feilipu/yaz180/docs/8255_crt_interface.png

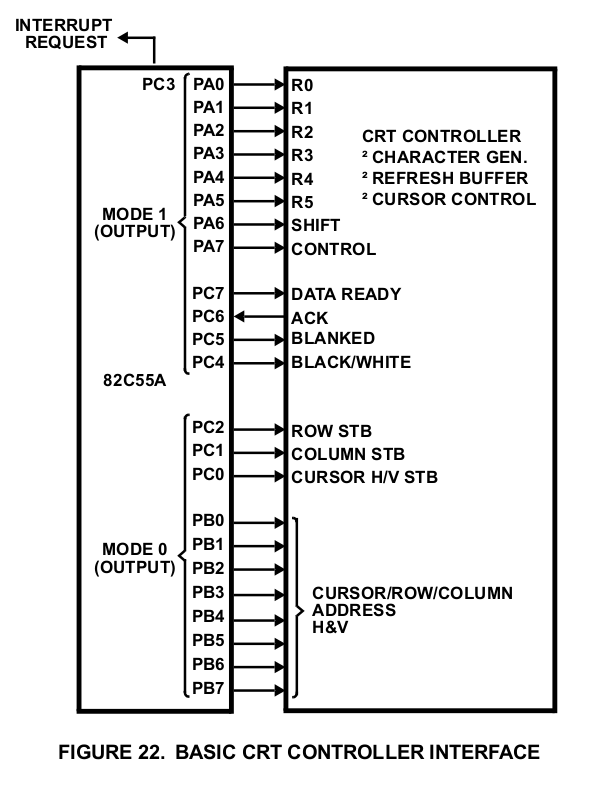
docs/8255_crt_interface.png
