feilipu/yaz180/docs/8255_floppy_disc_interface.png

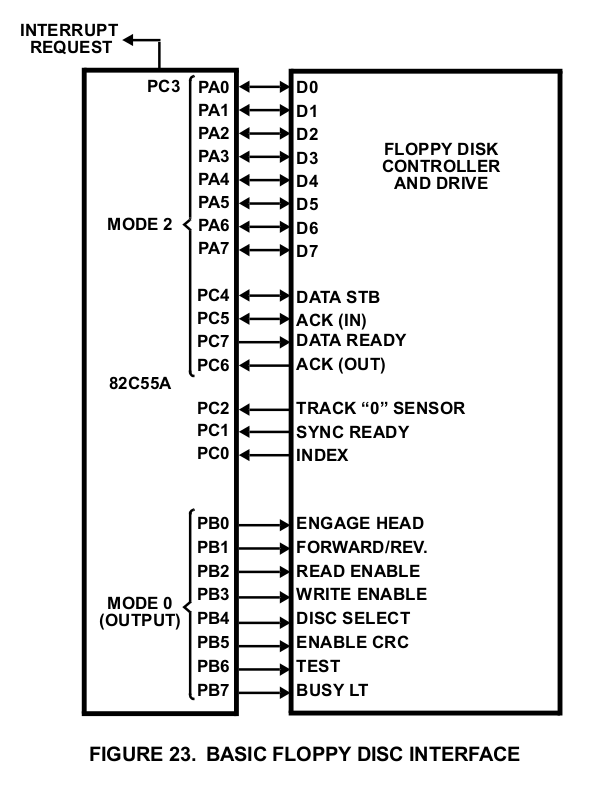
docs/8255_floppy_disc_interface.png
