feilipu/yaz180/docs/8255_keyboard_display_interface.png

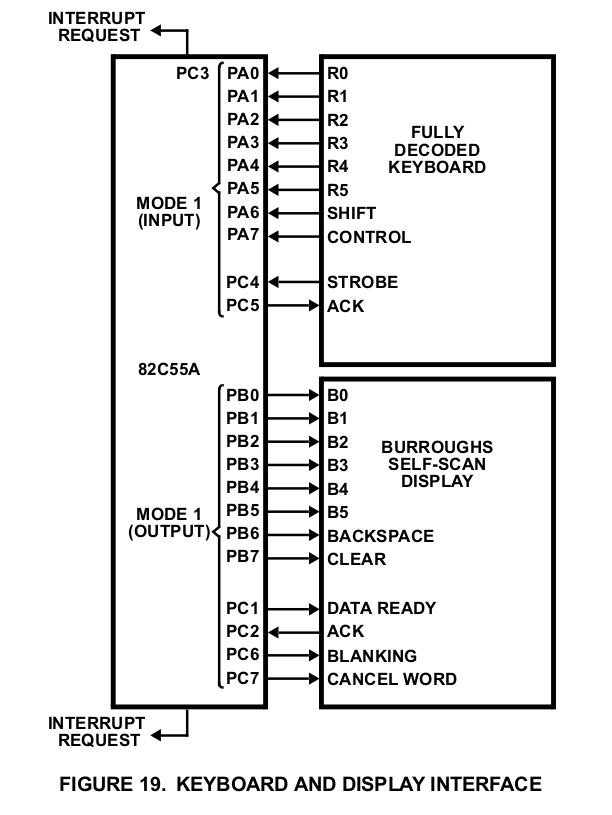
docs/8255_keyboard_display_interface.png
