feilipu/yaz180/docs/8255_keyboard_terminal_interface.png

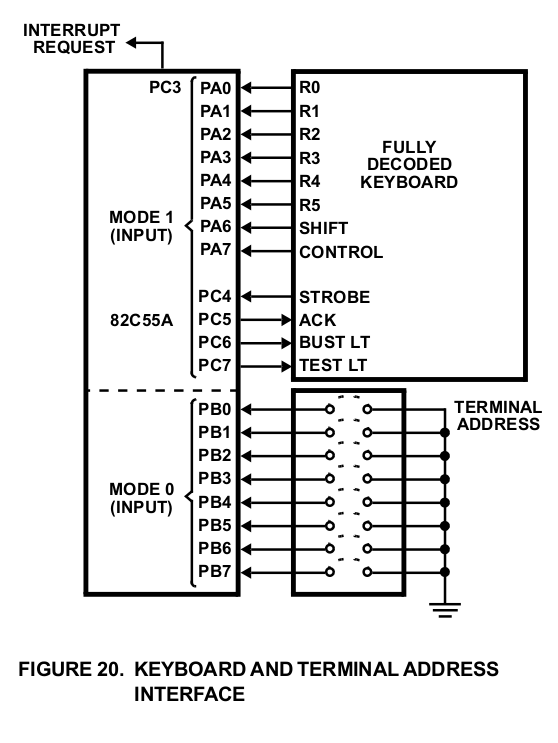
docs/8255_keyboard_terminal_interface.png
