feilipu/yaz180/docs/IMG_0698.JPG

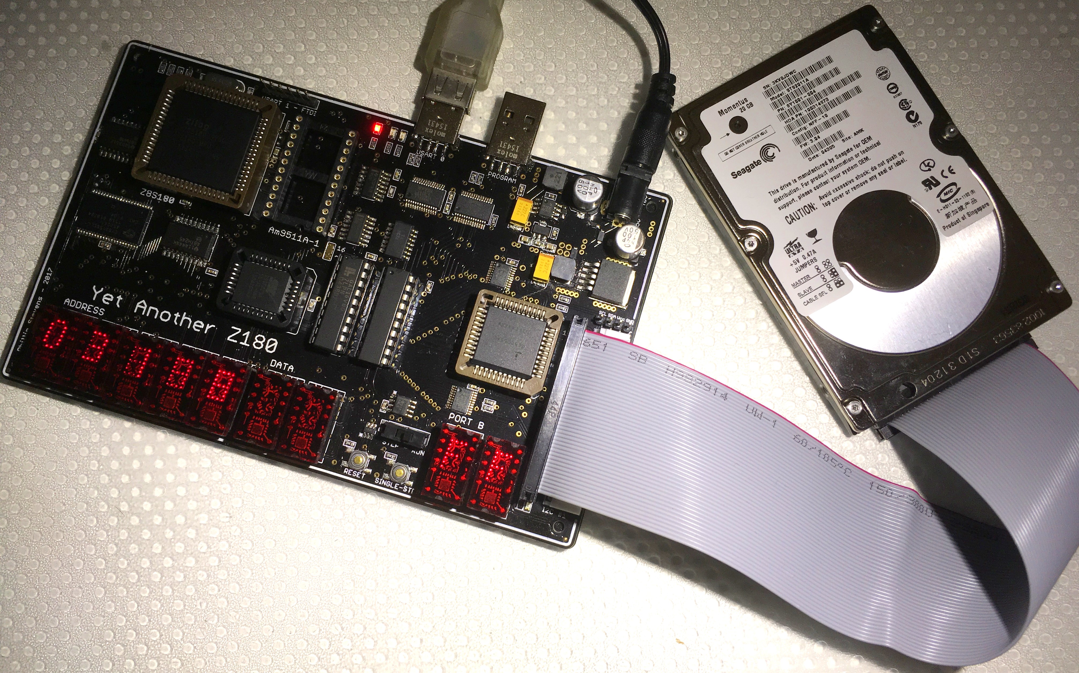
docs/IMG_0698.JPG
