feilipu/yaz180/docs/inter_bank_call.png

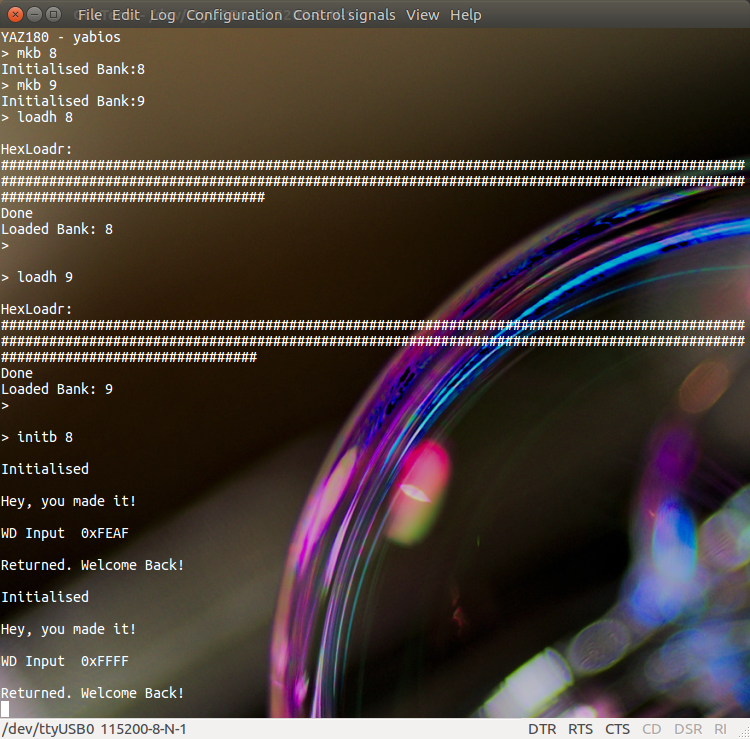
docs/inter_bank_call.png
