feilipu/yaz180/docs/LOGIC_PLD_A.png

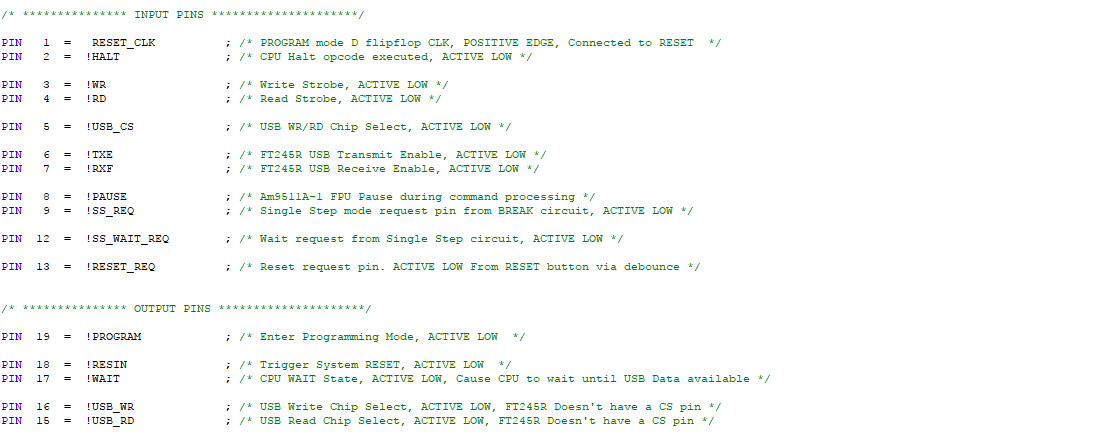
docs/LOGIC_PLD_A.png
