feilipu/yaz180/docs/LOGIC_PLD_B.png

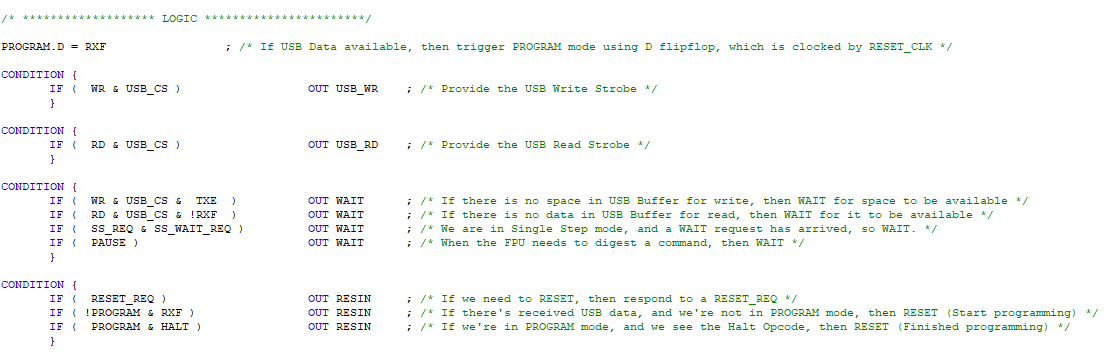
docs/LOGIC_PLD_B.png
