feilipu/yaz180/docs/MEMORY_PLD_2018_A.png

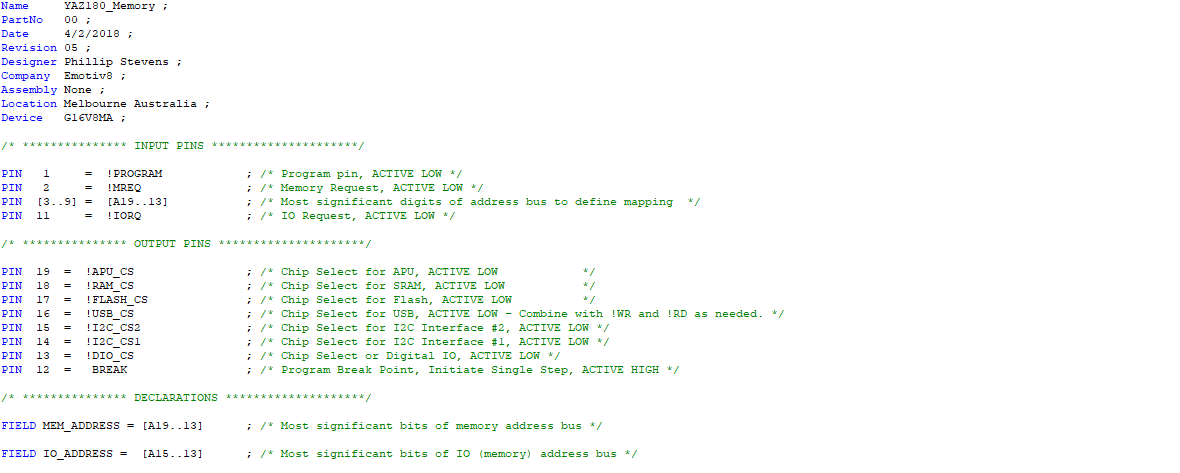
docs/MEMORY_PLD_2018_A.png
