feilipu/yaz180/docs/MEMORY_PLD_2018_B.png

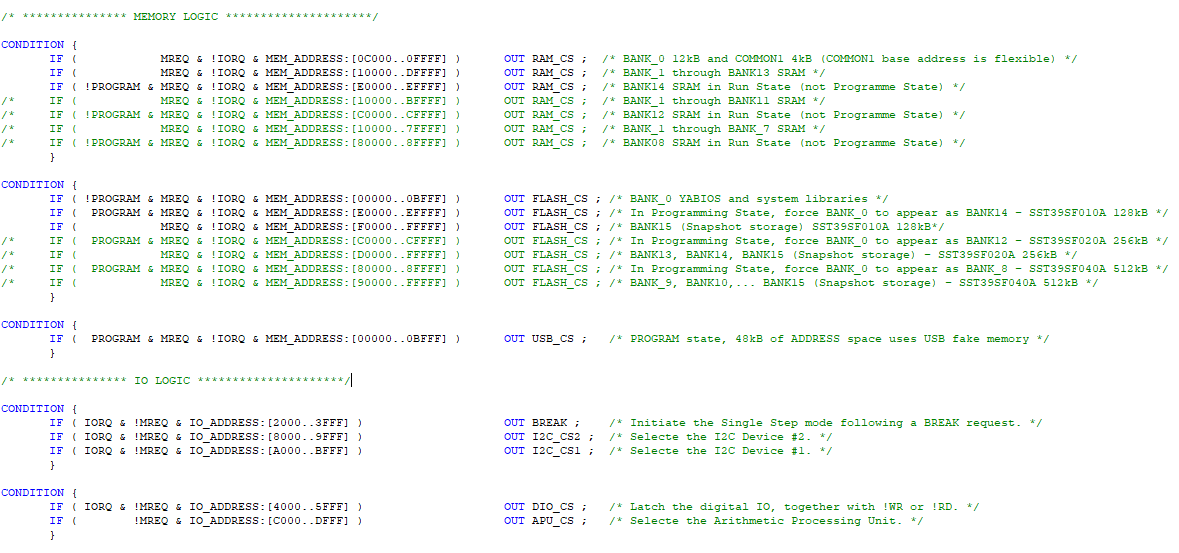
docs/MEMORY_PLD_2018_B.png
