feilipu/yaz180/docs/P1080759.JPG

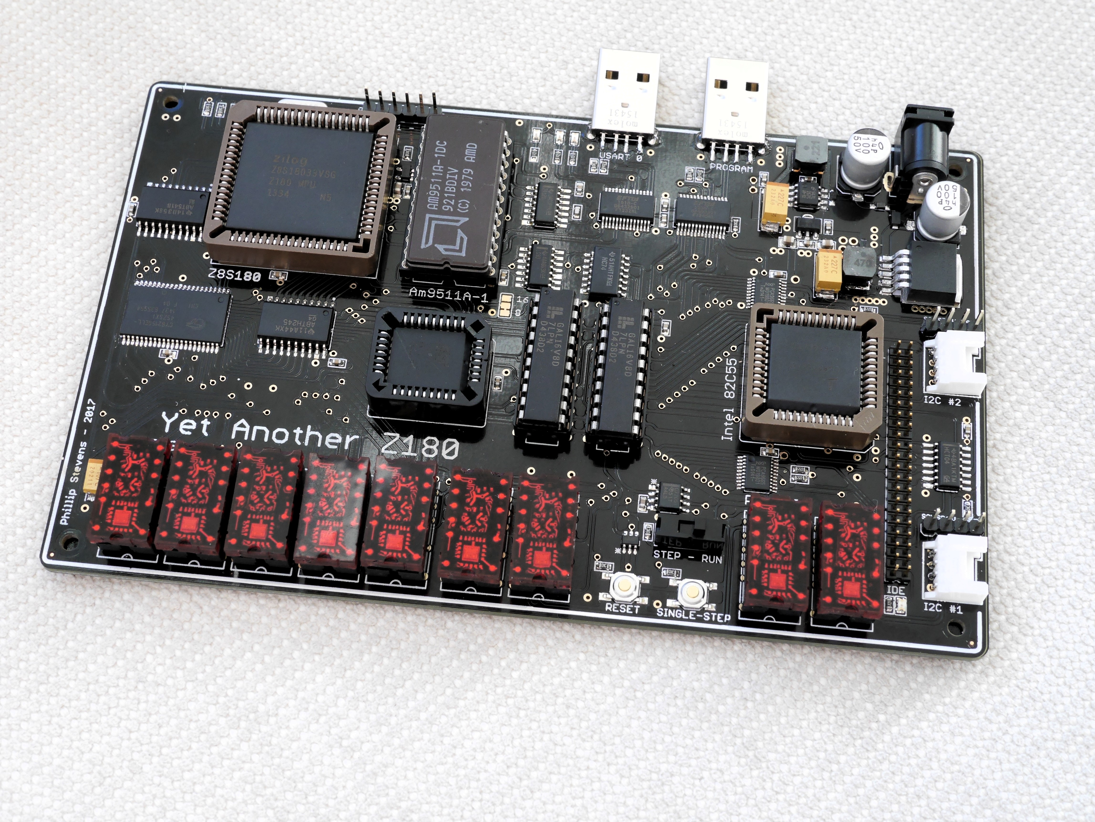
docs/P1080759.JPG
