feilipu/yaz180/docs/P1080760.JPG

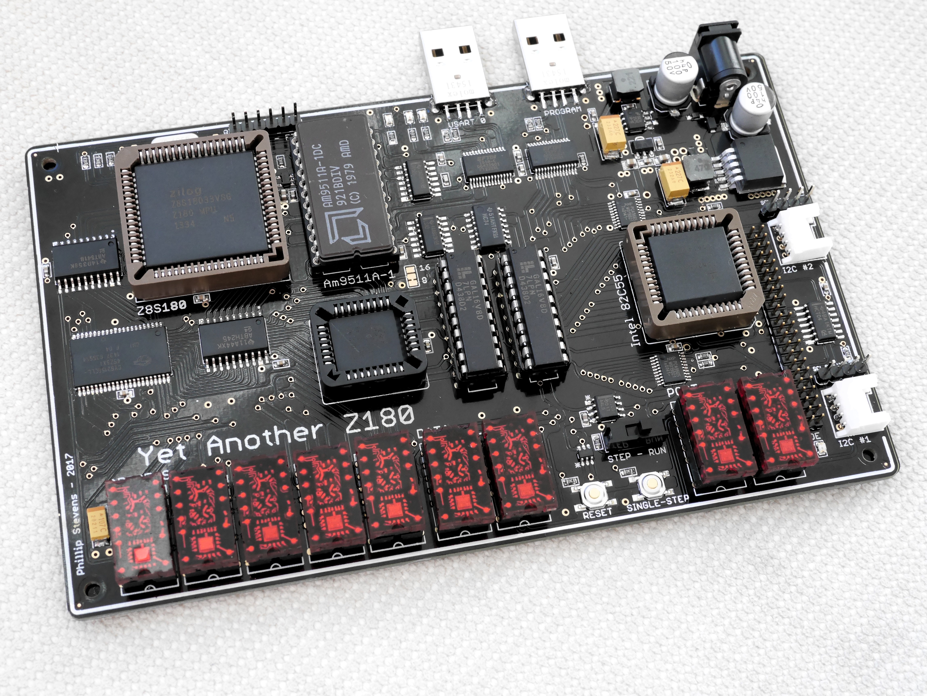
docs/P1080760.JPG
