feilipu/yaz180/docs/P1080761.JPG

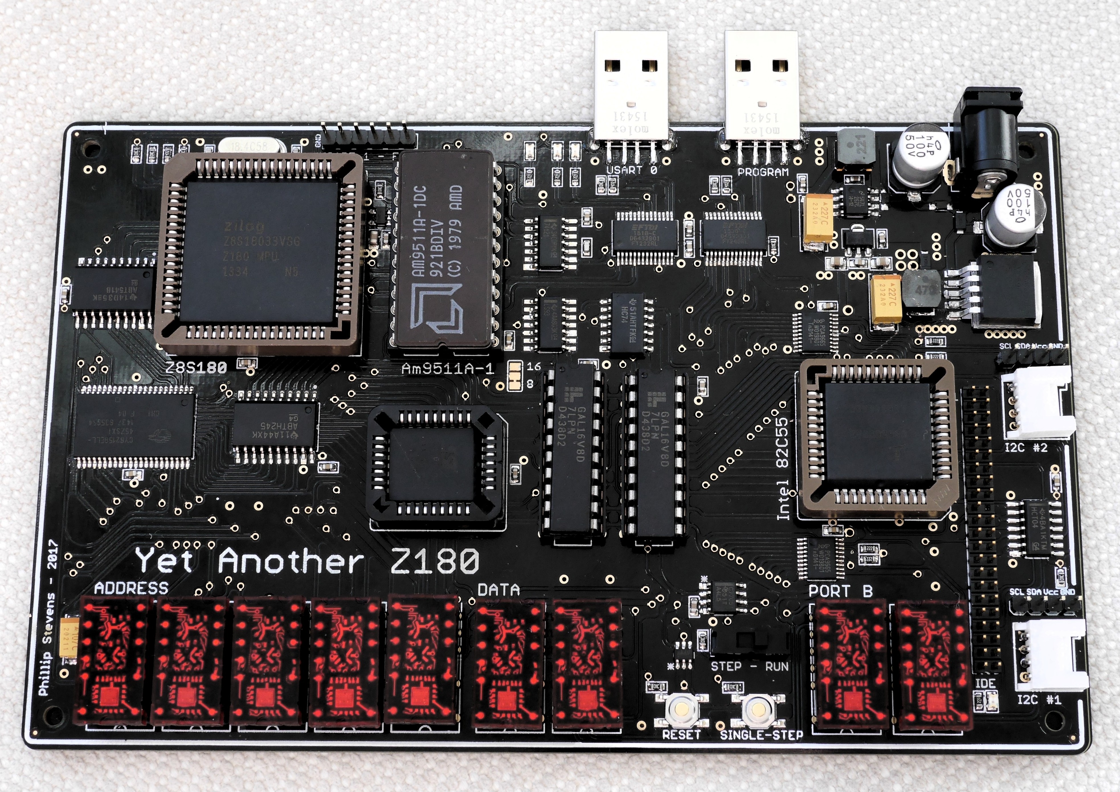
docs/P1080761.JPG
