feilipu/yaz180/docs/P1090698.JPG

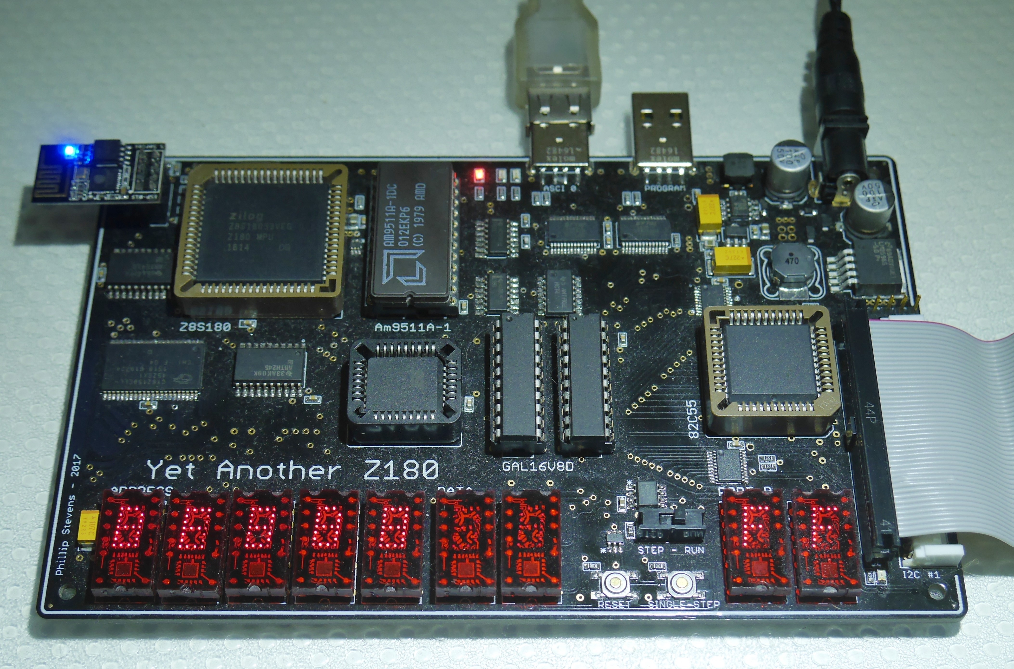
docs/P1090698.JPG
