feilipu/yaz180/docs/P1090699.JPG

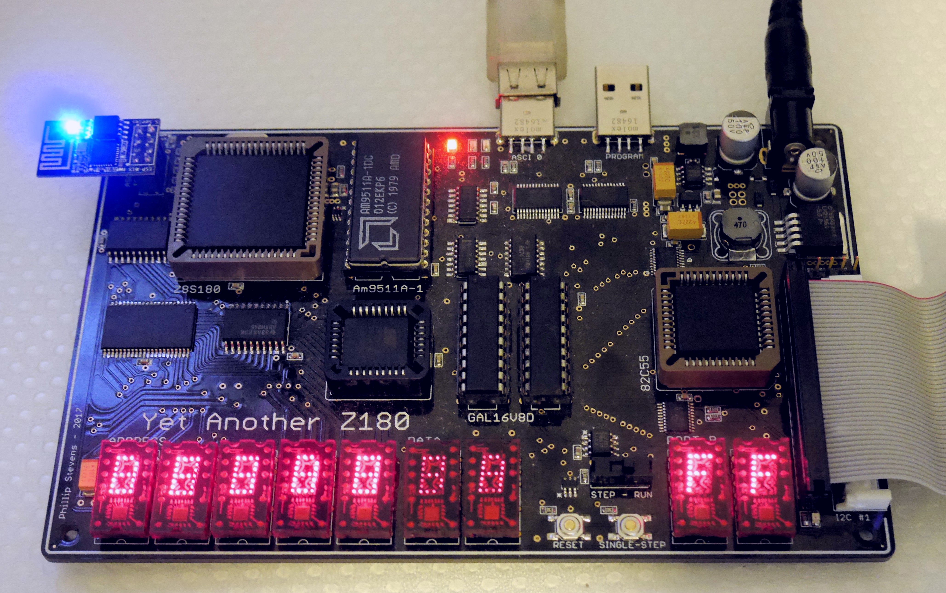
docs/P1090699.JPG
