feilipu/yaz180/docs/yaz180_cpm22.png

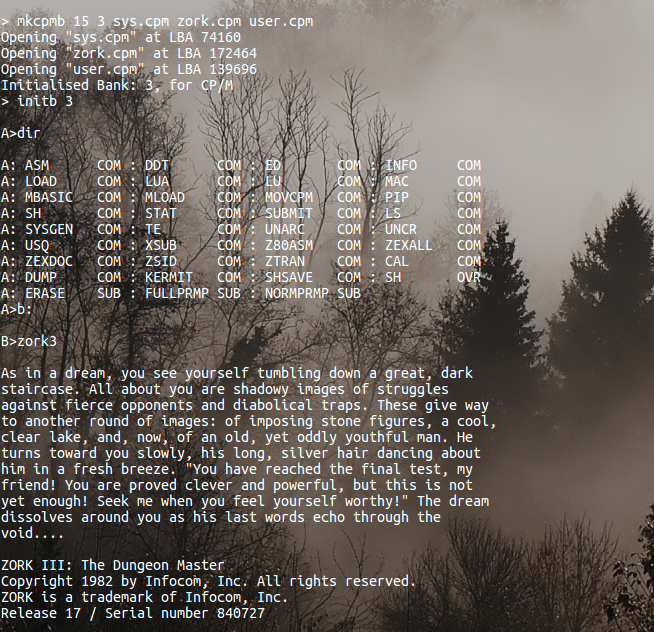
docs/yaz180_cpm22.png
