feilipu/yaz180/docs/yaz180_cpm.png

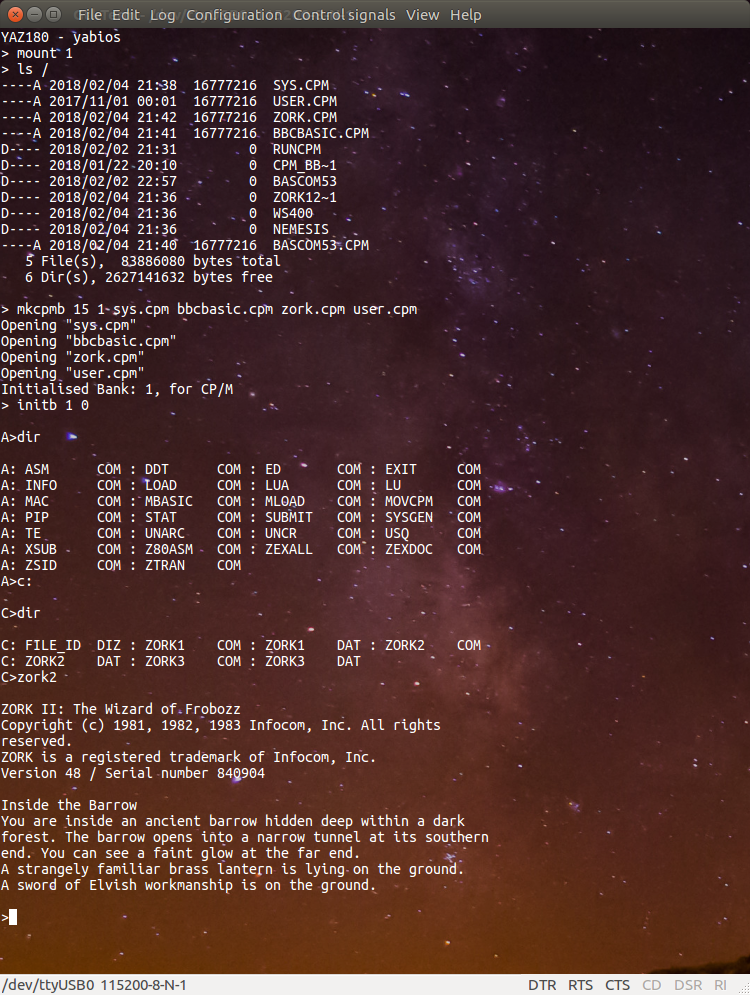
docs/yaz180_cpm.png
