feilipu/yaz180/docs/YAZ180v2.2.png

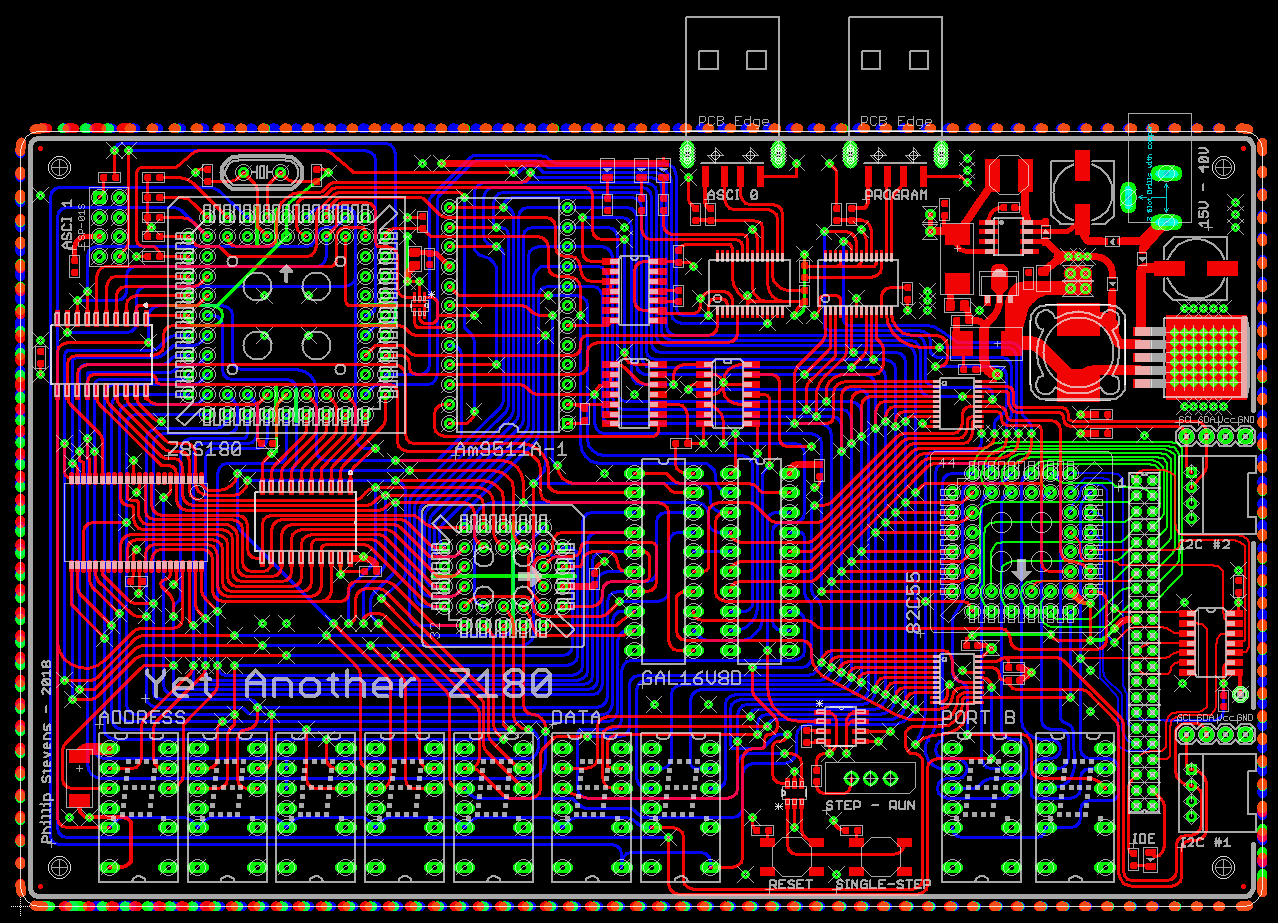
docs/YAZ180v2.2.png
