feilipu/yaz180/docs/YAZ180v21_front.JPG

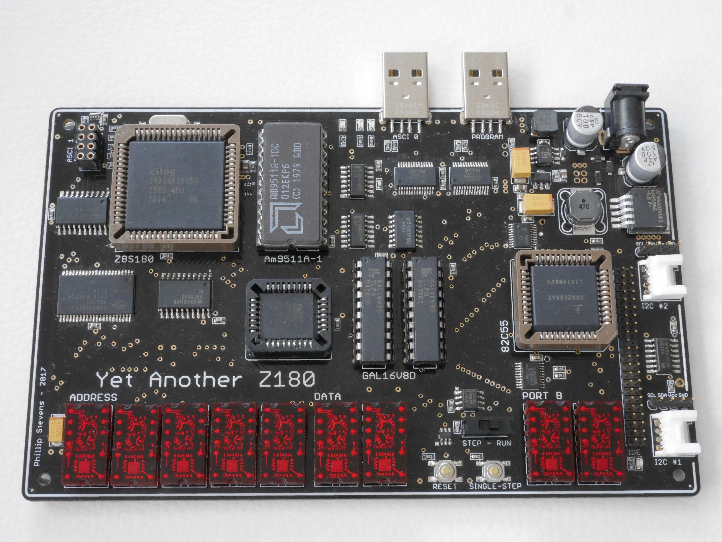
docs/YAZ180v21_front.JPG
