feilipu/yaz180/docs/YAZ180v21_left.JPG

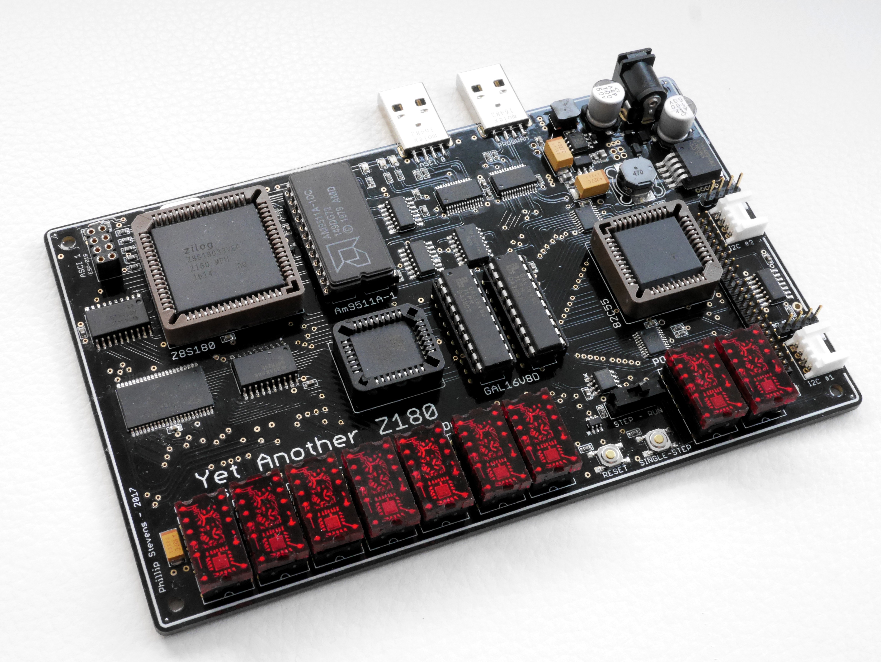
docs/YAZ180v21_left.JPG
