feilipu/yaz180/docs/YAZ180v21_left_low.JPG

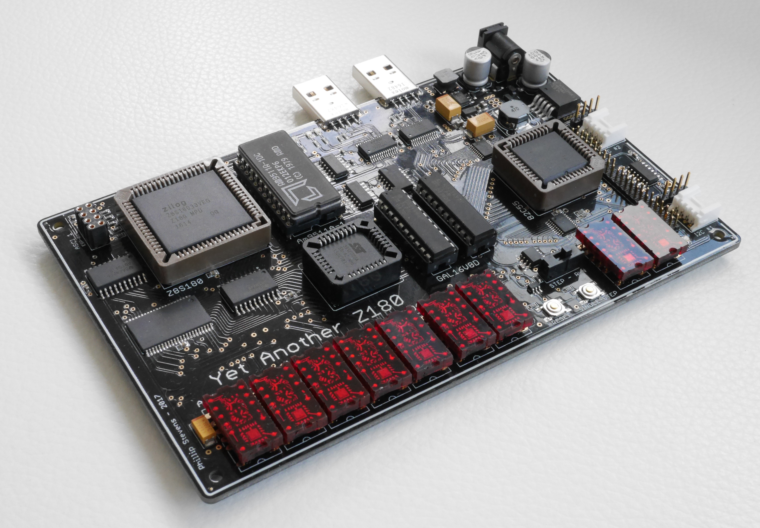
docs/YAZ180v21_left_low.JPG
