feilipu/yaz180/docs/YAZ180v21_right_low.JPG

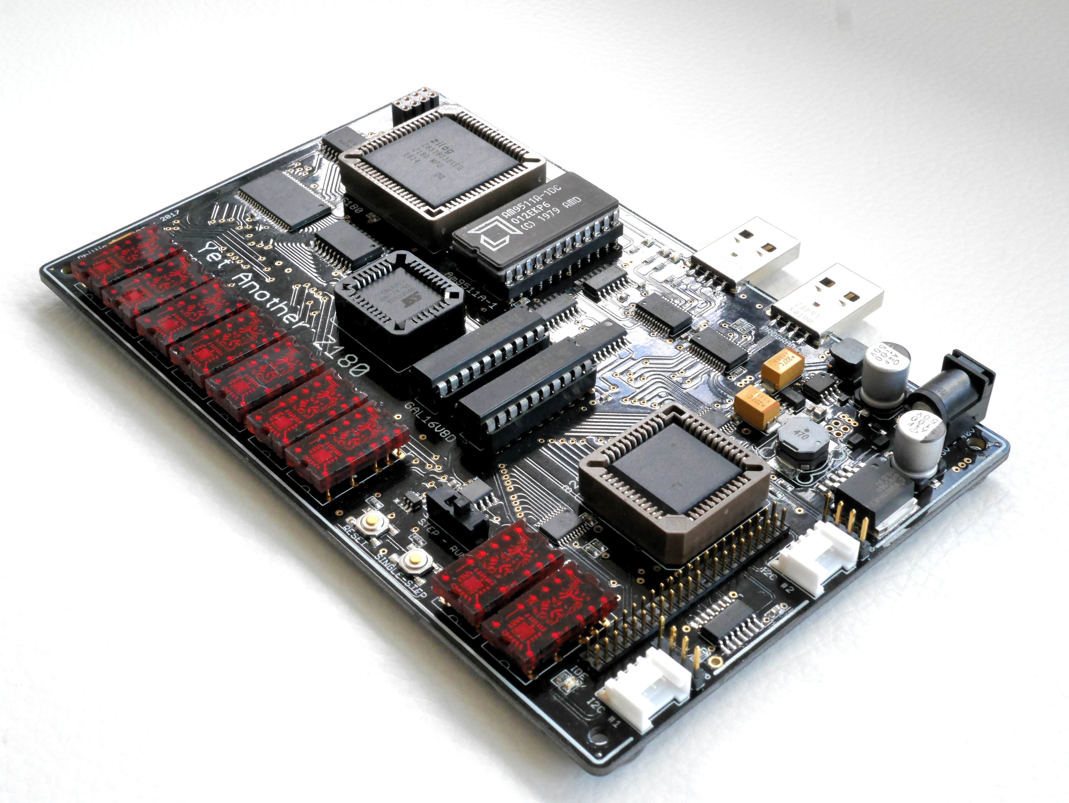
docs/YAZ180v21_right_low.JPG
