feilipu/yaz180/docs/YAZ180v21_scale.JPG

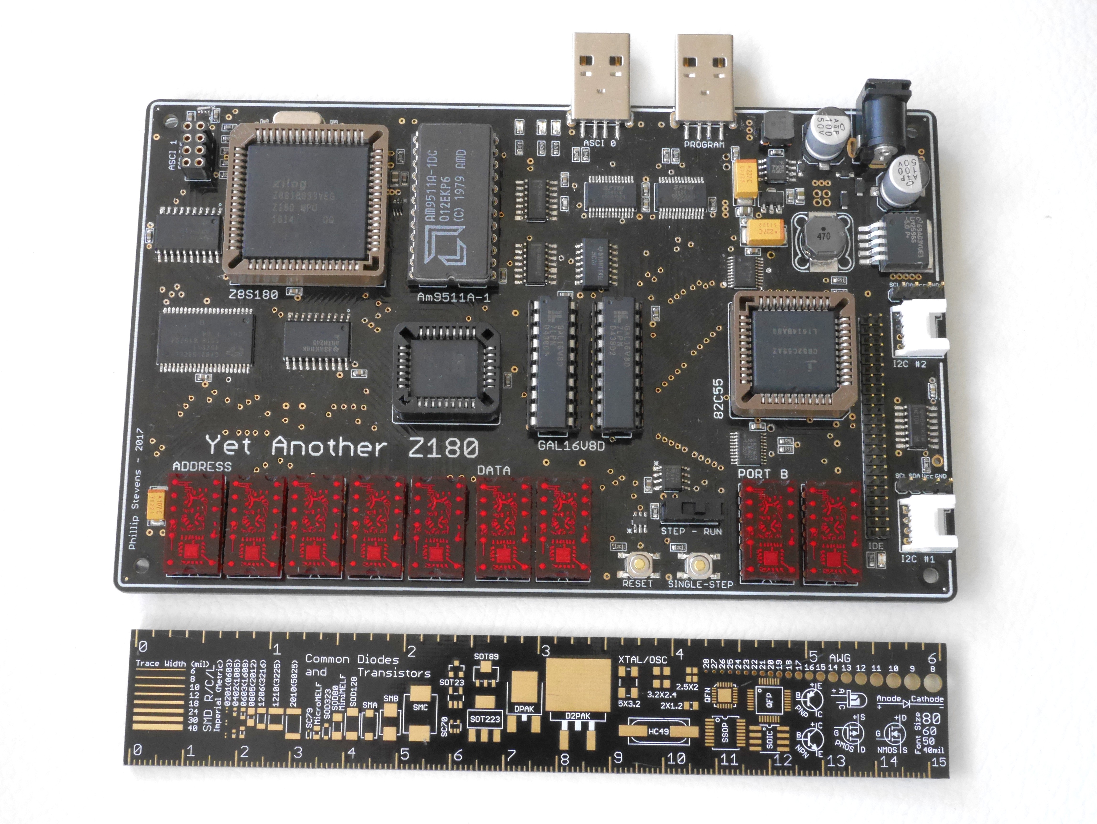
docs/YAZ180v21_scale.JPG
