feilipu/yaz180/docs/YAZ180v24_family.JPG

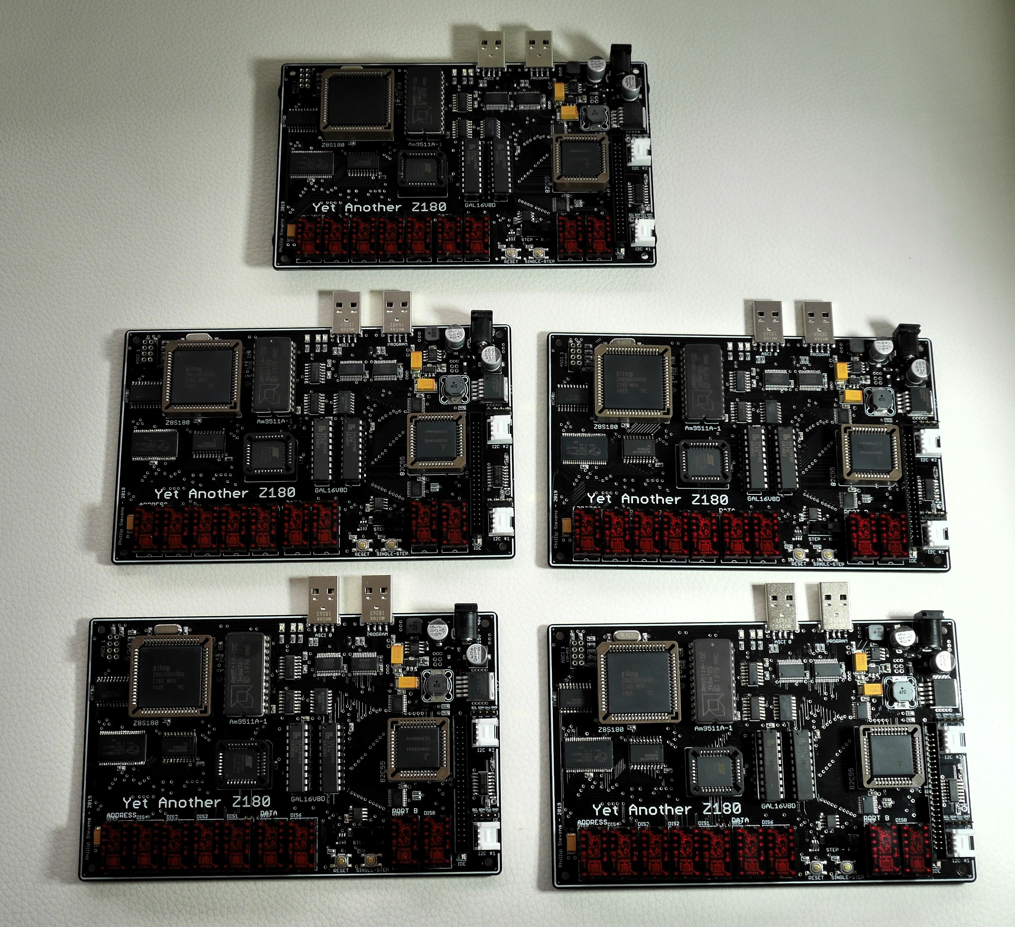
docs/YAZ180v24_family.JPG
