feilipu/yaz180/docs/YAZ180v24_front.JPG

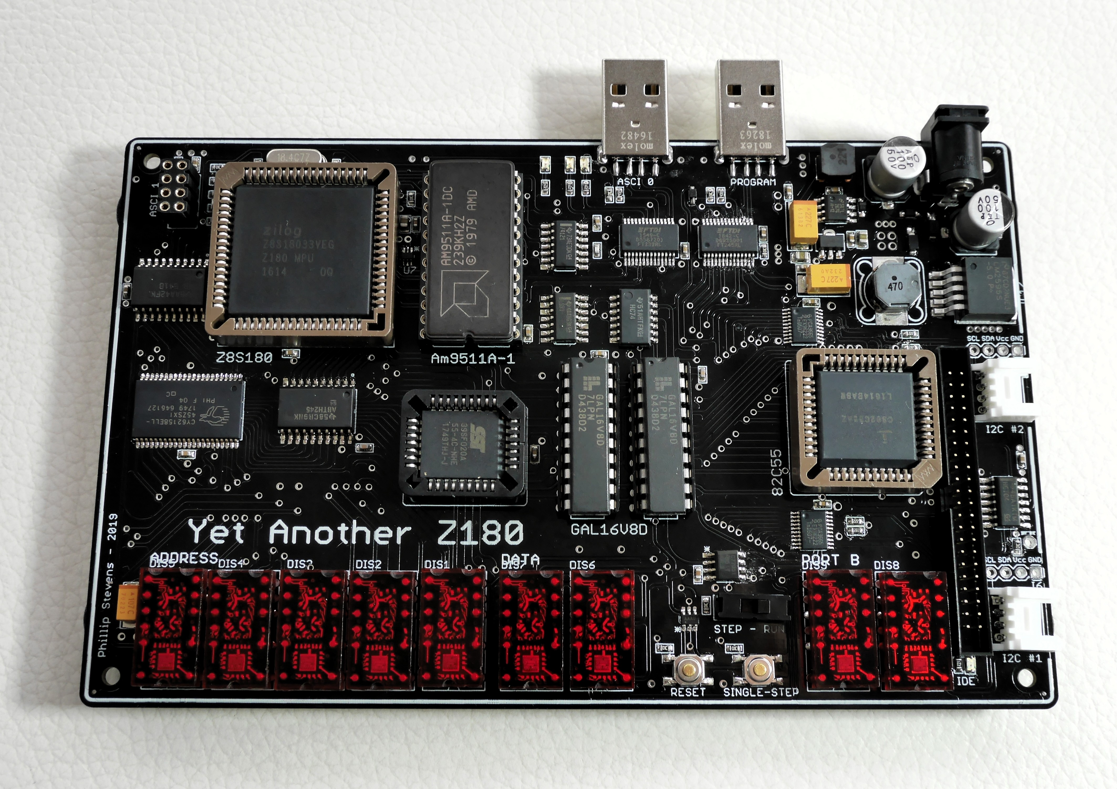
docs/YAZ180v24_front.JPG
