feilipu/yaz180/docs/8255_printer_interface.png

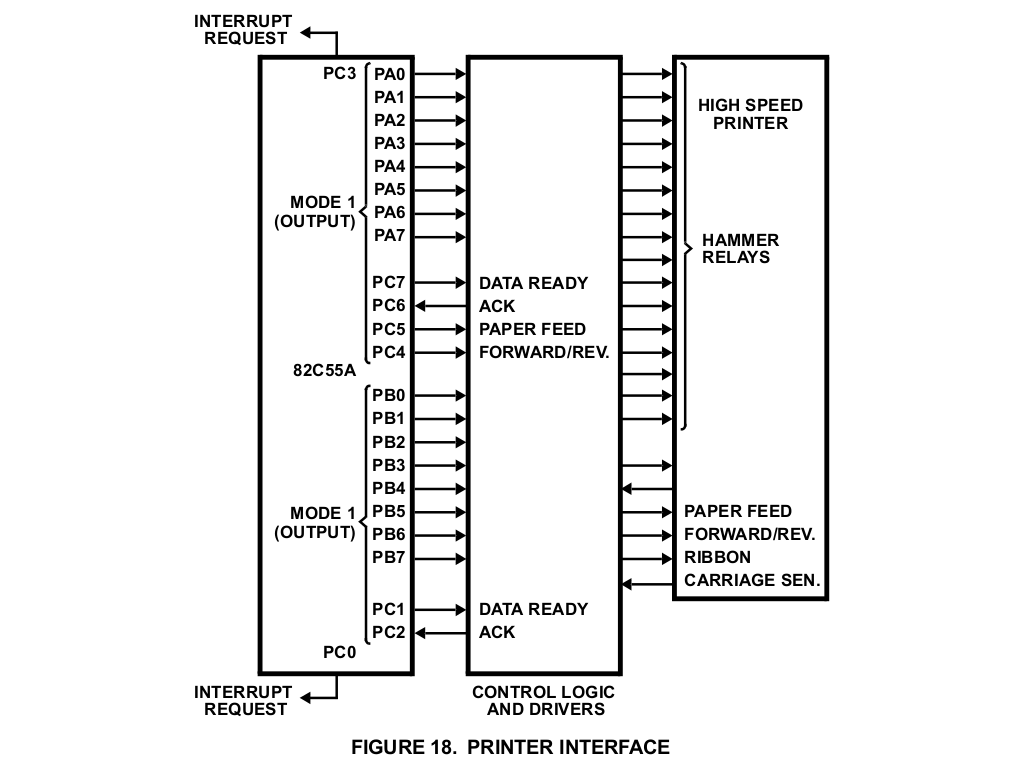
docs/8255_printer_interface.png
