feilipu/yaz180/pcb/V21_20171011/YAZ180_V21_All_Layers.pdf

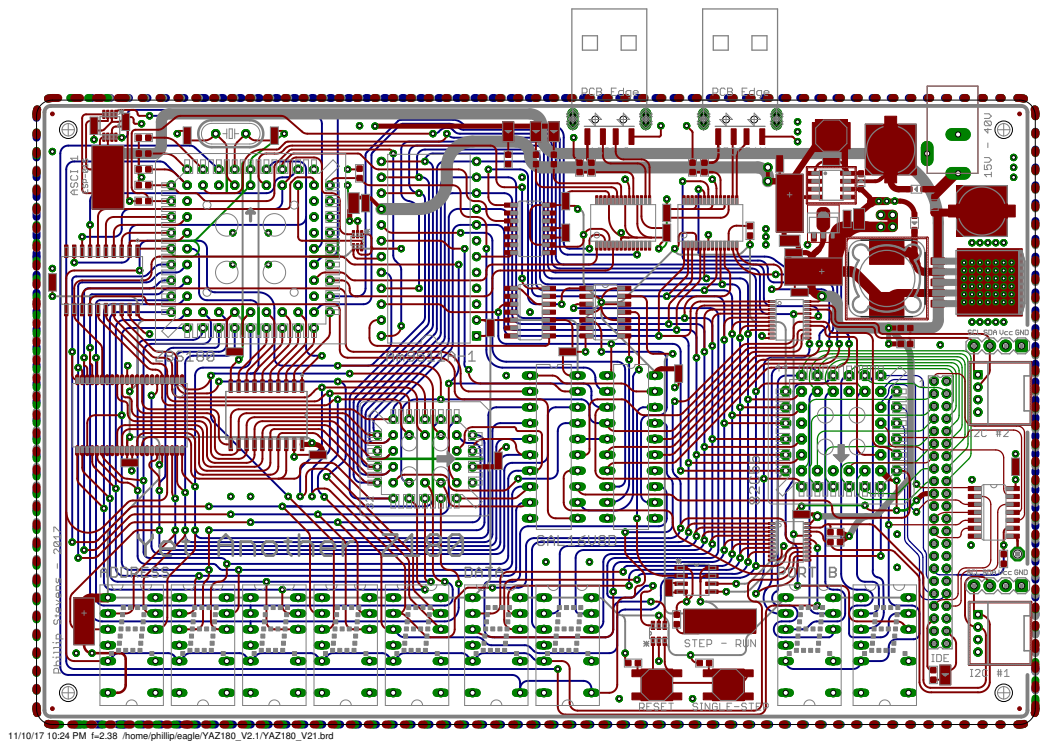
[picture p61: page 1]

11/10/17 10:24 PM f=2.38 /home/phillip/eagle/YAZ180_V2.1/YAZ180_V21.brd
