feilipu/yaz180/pcb/V21_20171011/YAZ180_V21_BottomLayer.pdf

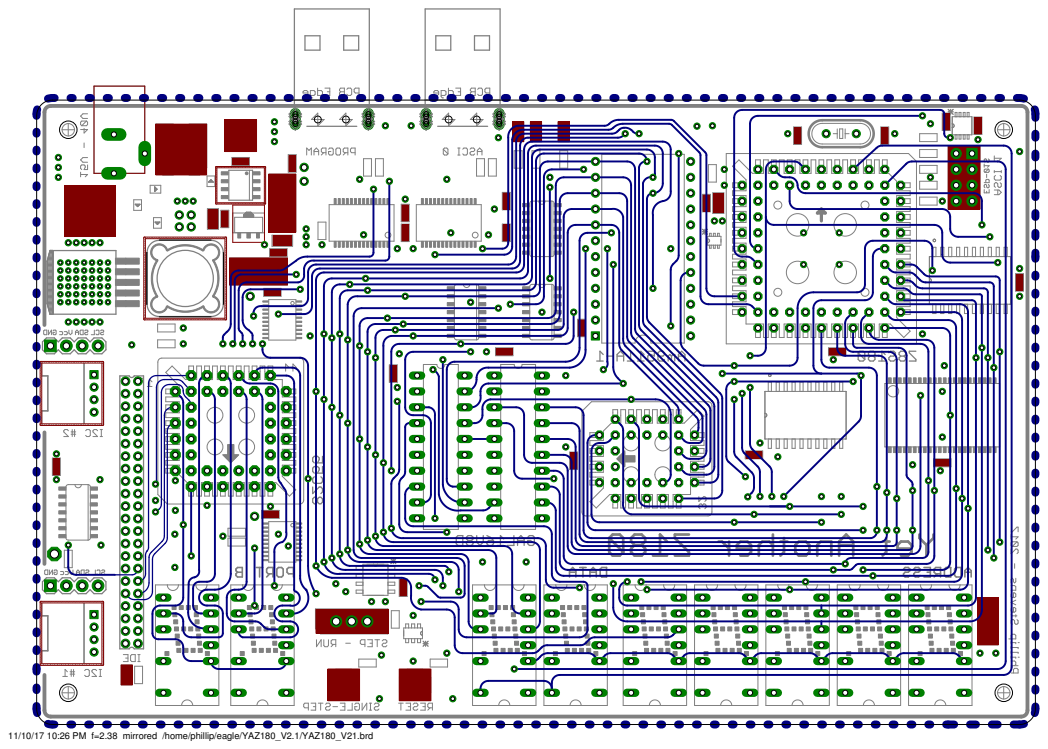
[picture p62: page 1]

11/10/17 10:26 PM f=2.38 mirrored /home/phillip/eagle/YAZ180_V2.1/YAZ180_V21.brd
