feilipu/yaz180/pcb/V21_20171011/YAZ180_V21_TopLayer.pdf

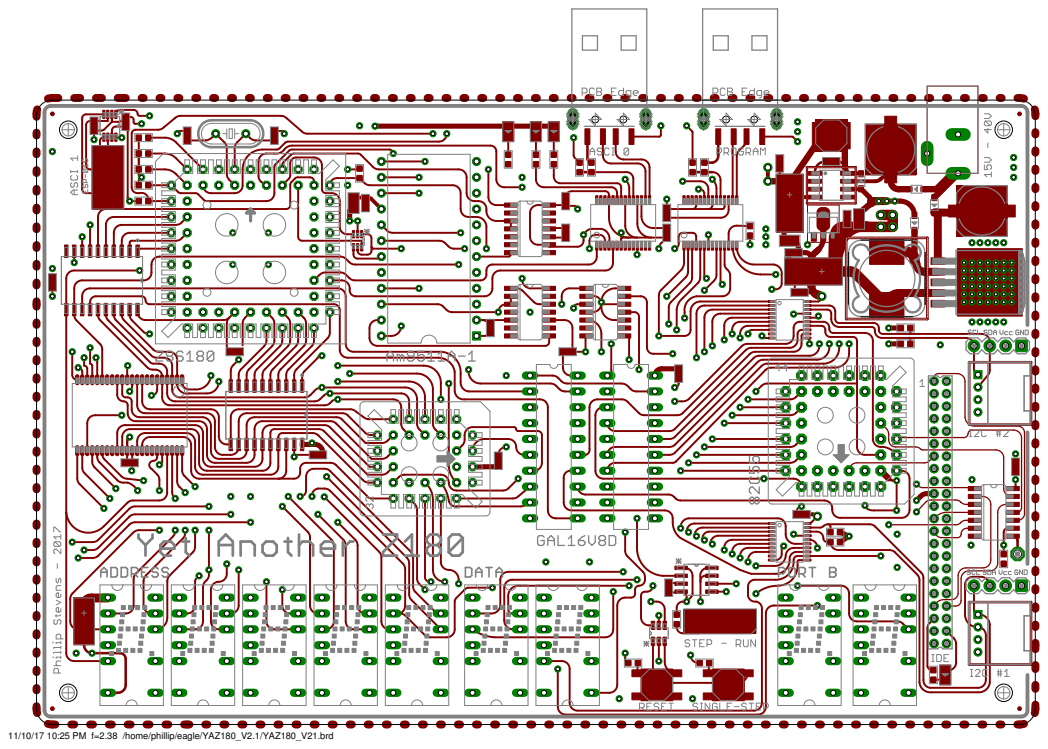
[picture p65: page 1]

11/10/17 10:25 PM f=2.38 /home/phillip/eagle/YAZ180_V2.1/YAZ180_V21.brd
