feilipu/yaz180/docs/YAZ180_V22_Schematic.pdf

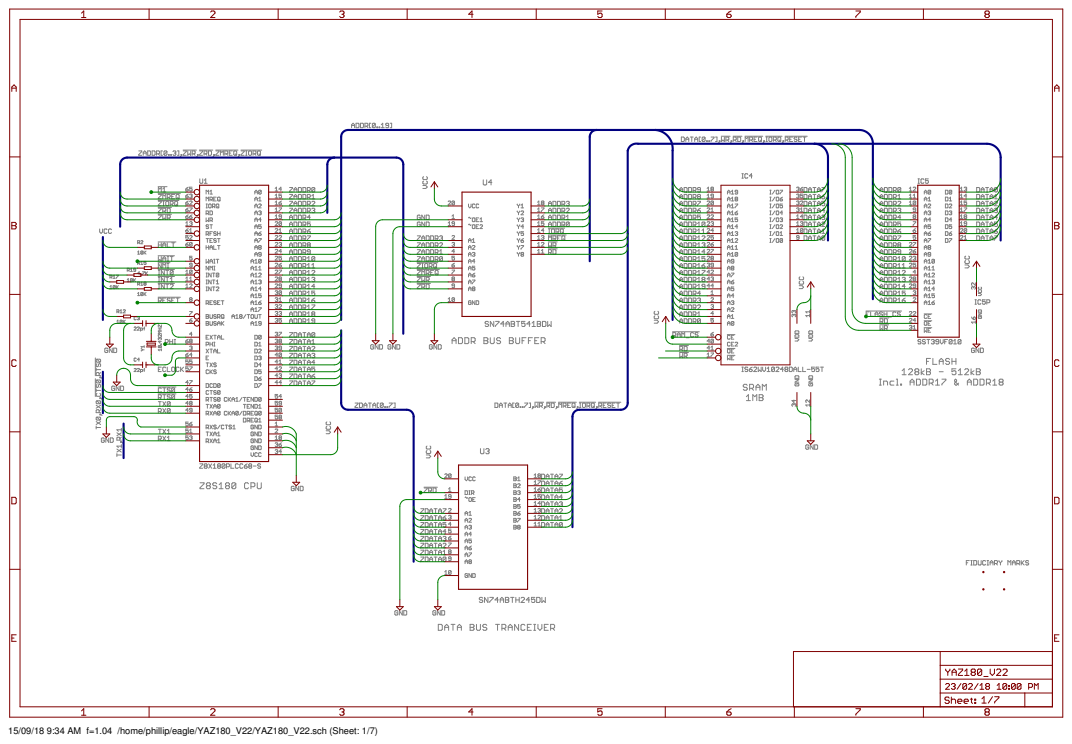
[picture p67: page 1]

15/09/18 9:34 AM f=1.04 /home/phillip/eagle/YAZ180_V22/YAZ180_V22.sch (Sheet: 1/7)

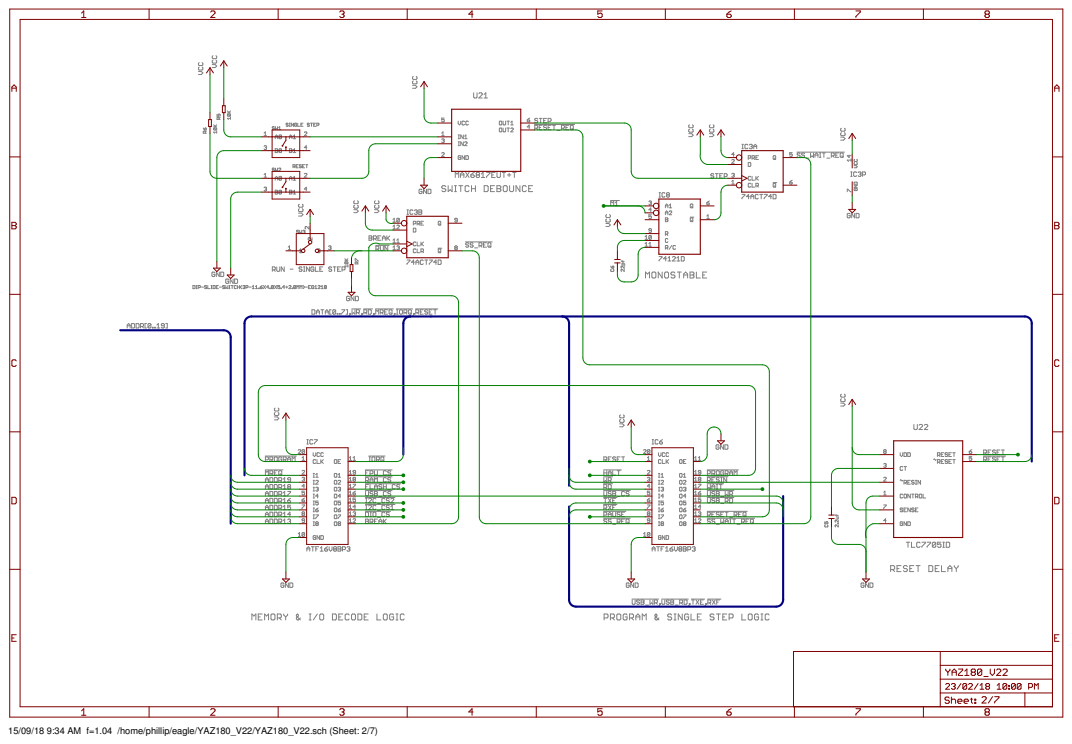
[picture p68: page 2]

15/09/18 9:34 AM f=1.04 /home/phillip/eagle/YAZ180_V22/YAZ180_V22.sch (Sheet: 2/7)

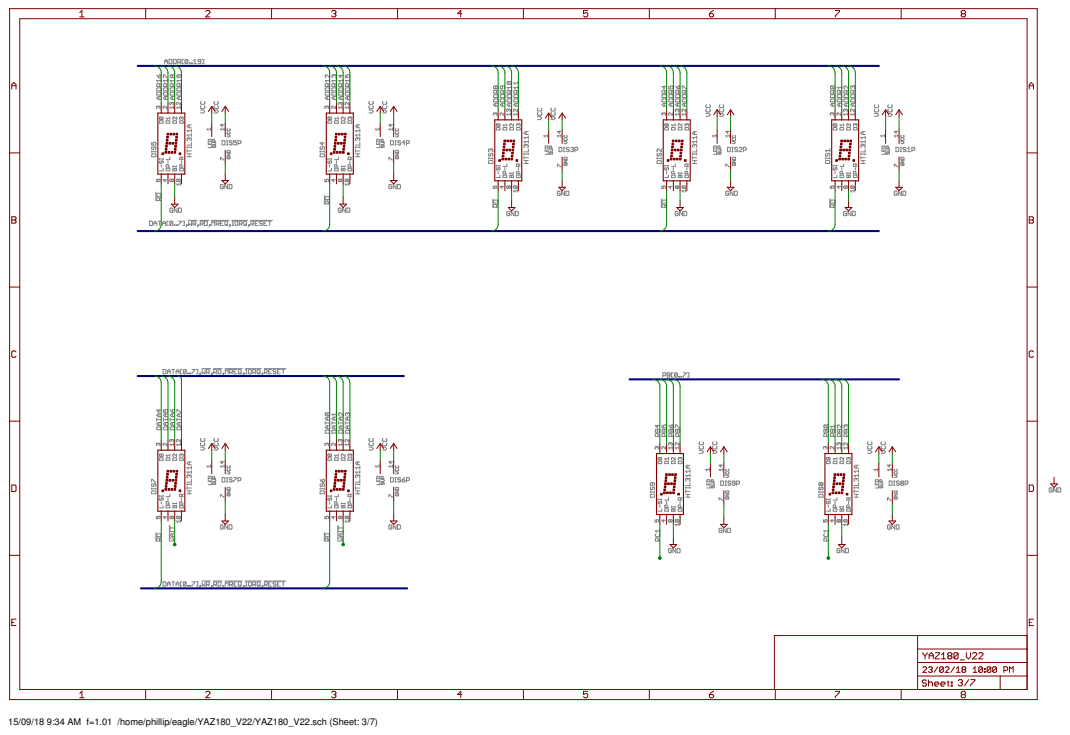
[picture p69: page 3]

15/09/18 9:34 AM f=1.01 /home/phillip/eagle/YAZ180_V22/YAZ180_V22.sch (Sheet: 3/7)

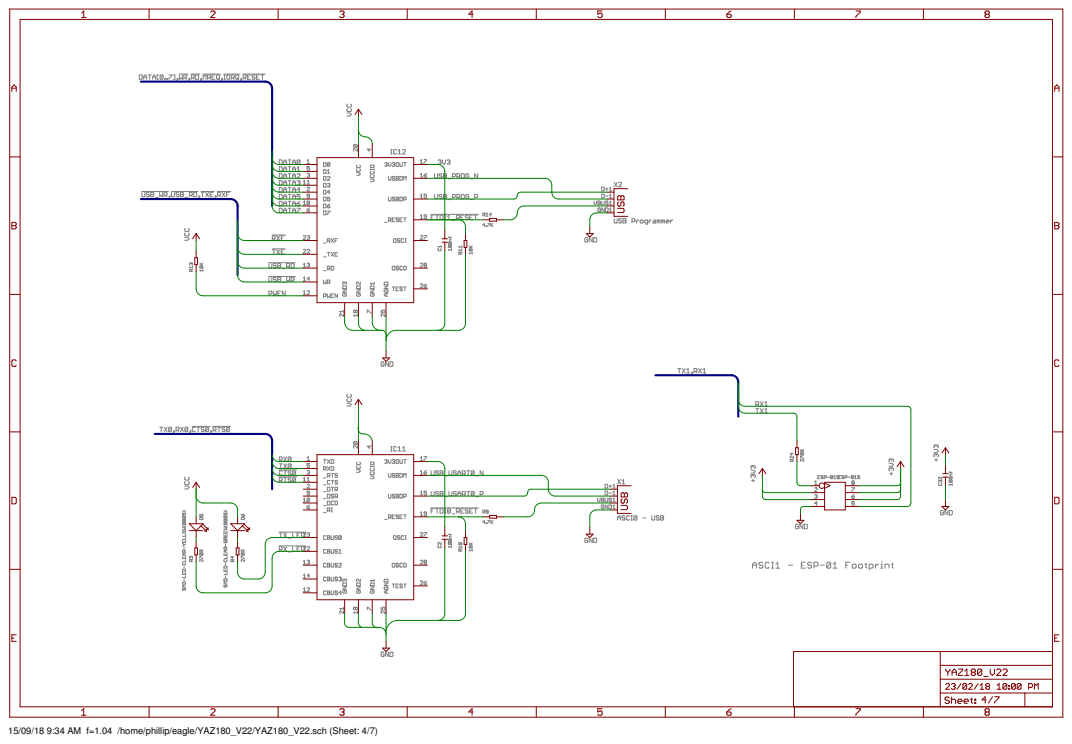
[picture p70: page 4]

15/09/18 9:34 AM f=1.04 /home/phillip/eagle/YAZ180_V22/YAZ180_V22.sch (Sheet: 4/7)

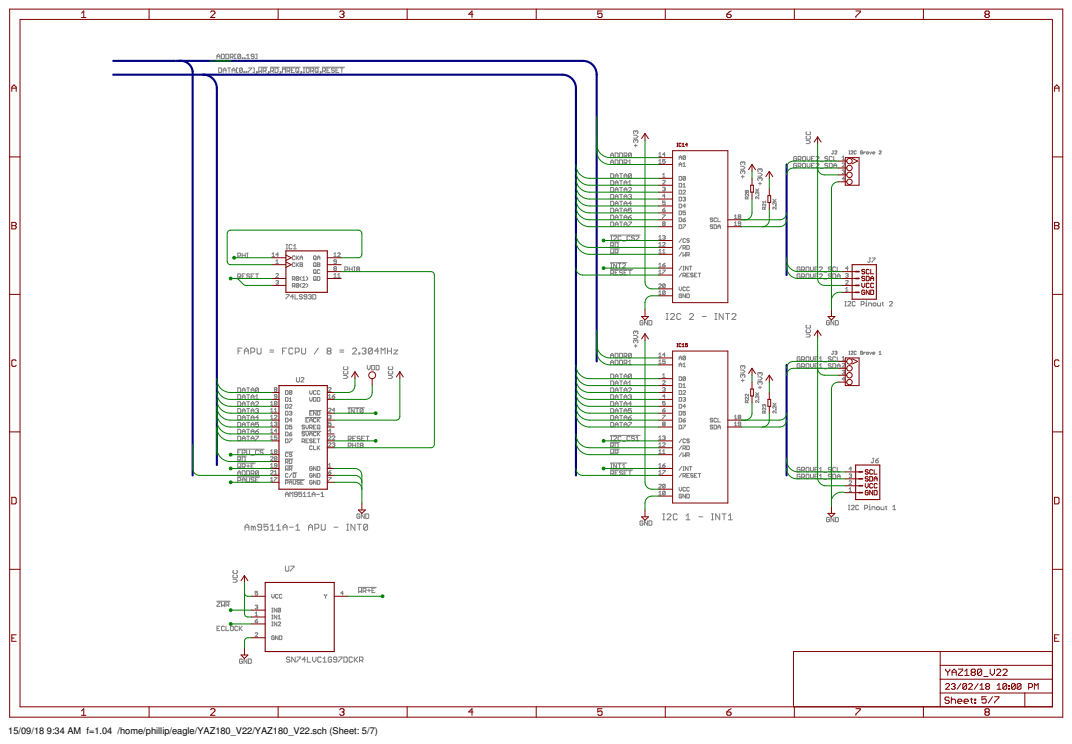
[picture p71: page 5]

15/09/18 9:34 AM f=1.04 /home/phillip/eagle/YAZ180_V22/YAZ180_V22.sch (Sheet: 5/7)

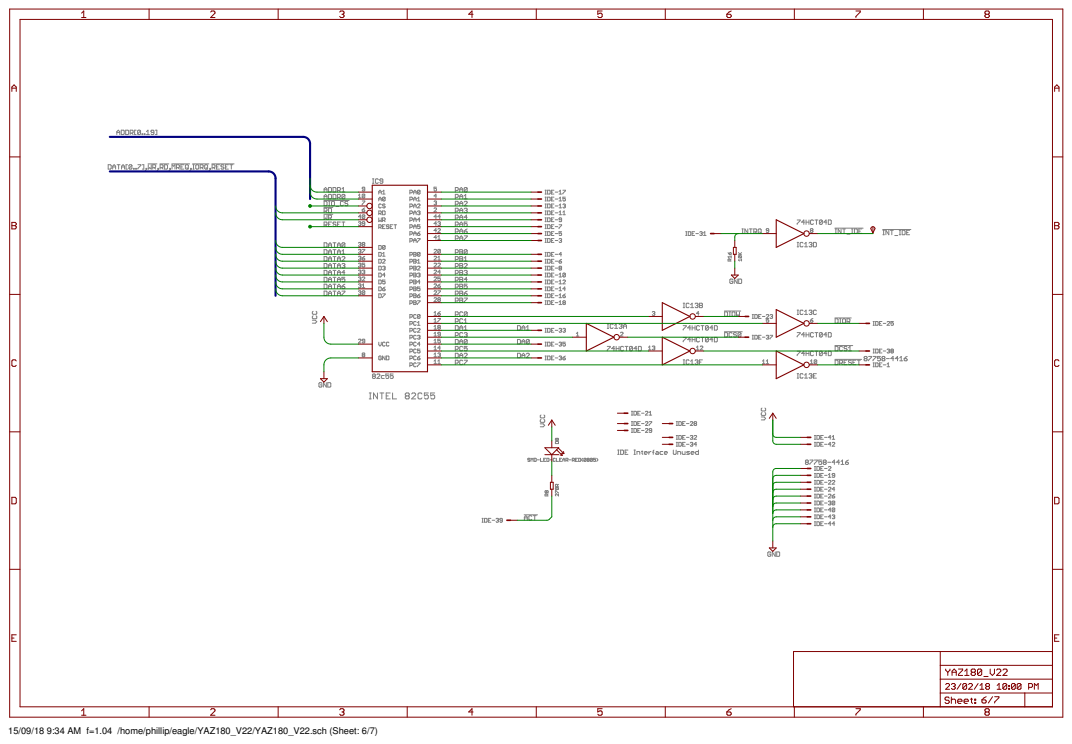
[picture p72: page 6]

15/09/18 9:34 AM f=1.04 /home/phillip/eagle/YAZ180_V22/YAZ180_V22.sch (Sheet: 6/7)

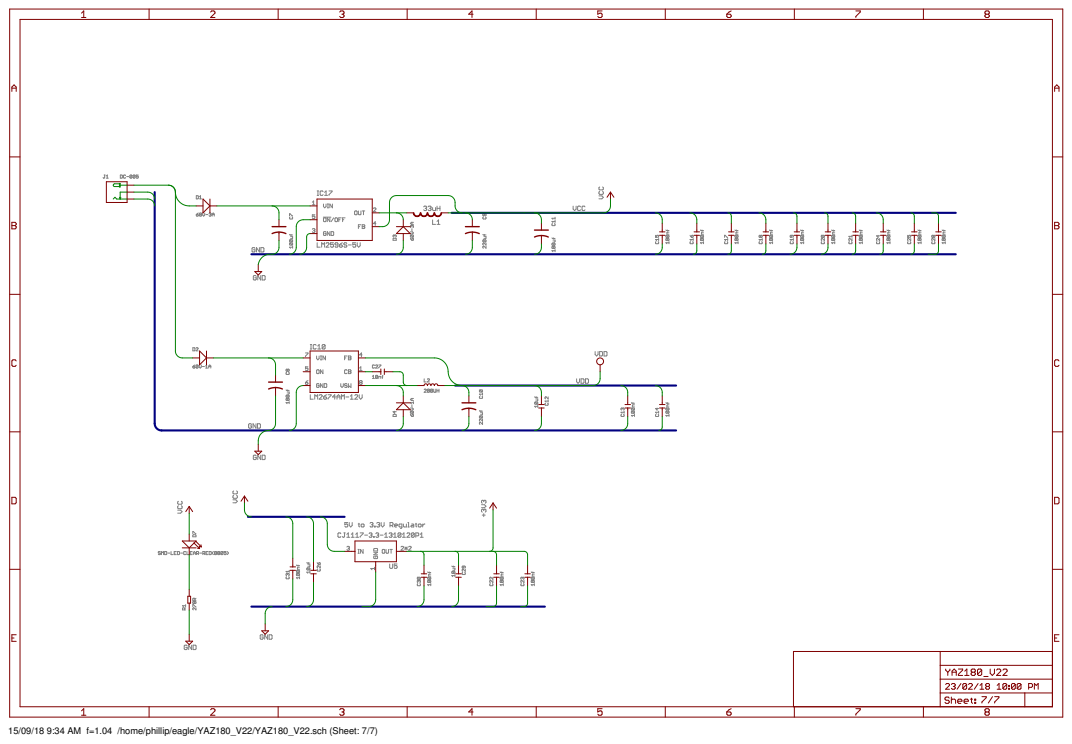
[picture p73: page 7]

15/09/18 9:34 AM f=1.04 /home/phillip/eagle/YAZ180_V22/YAZ180_V22.sch (Sheet: 7/7)
