feilipu/yaz180/docs/YAZ180_V21_Schematic.pdf

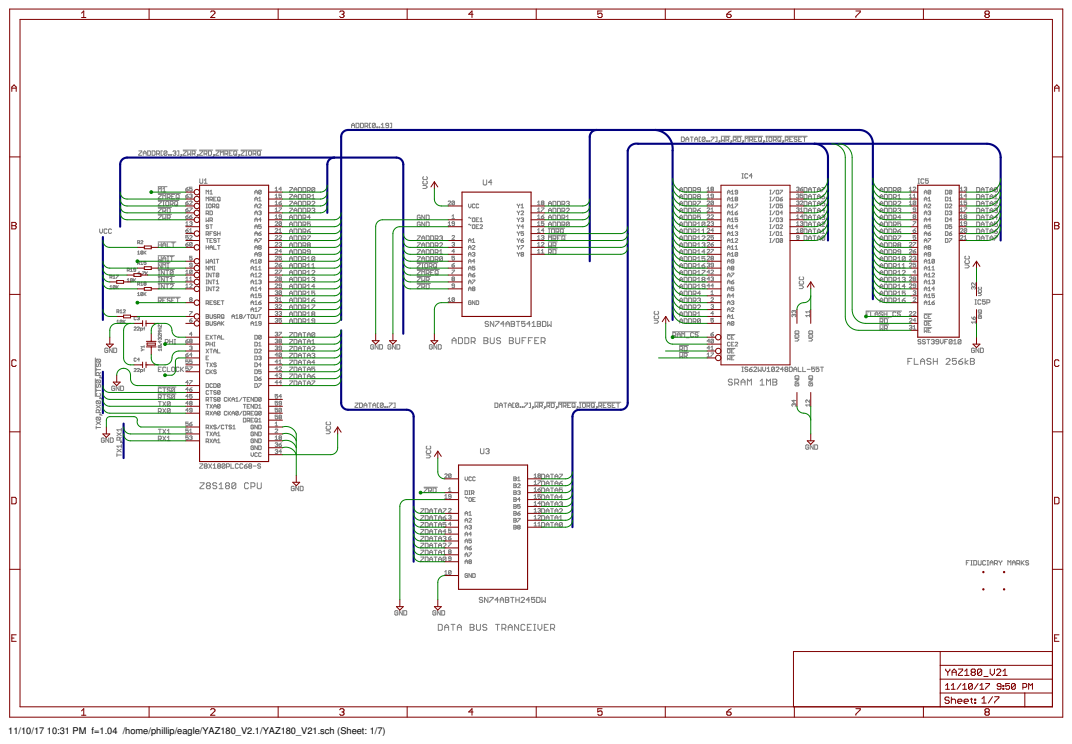
[picture p74: page 1]

11/10/17 10:31 PM f=1.04 /home/phillip/eagle/YAZ180_V2.1/YAZ180_V21.sch (Sheet: 1/7)

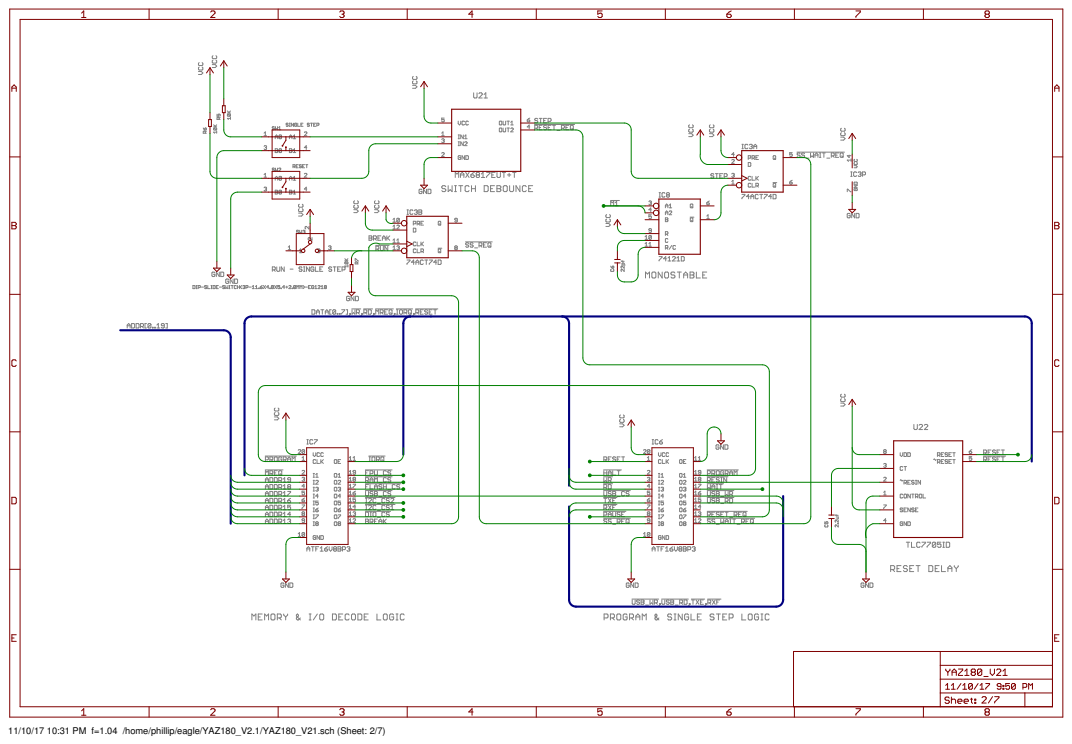
[picture p75: page 2]

11/10/17 10:31 PM f=1.04 /home/phillip/eagle/YAZ180_V2.1/YAZ180_V21.sch (Sheet: 2/7)

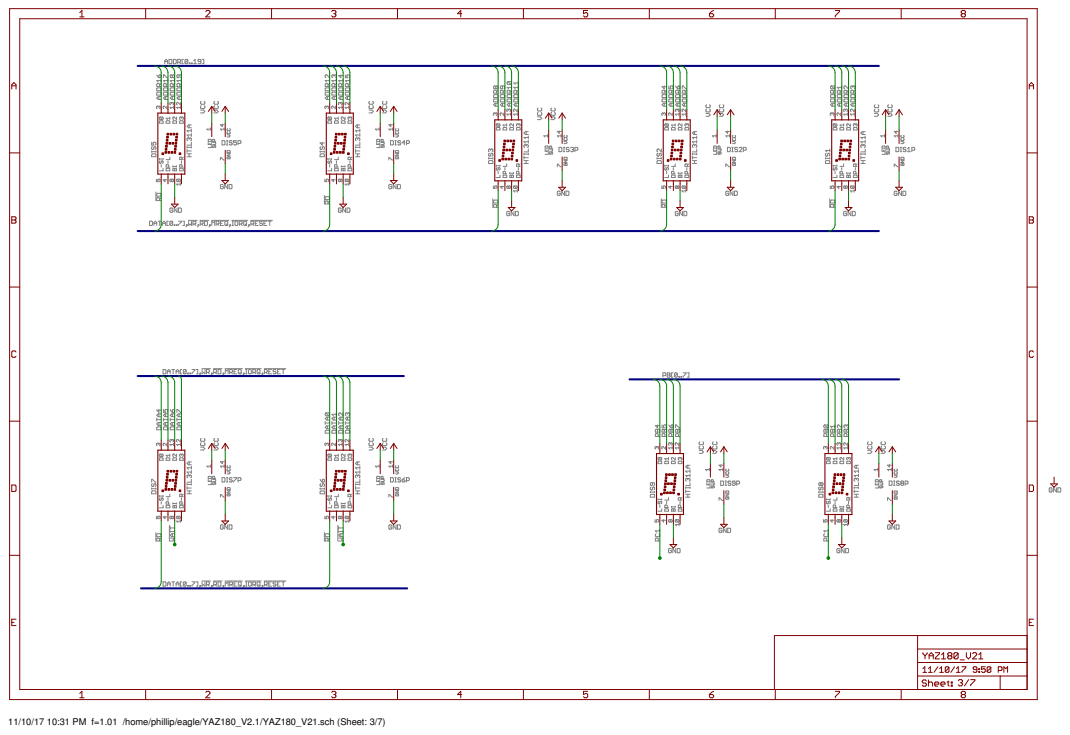
[picture p76: page 3]

11/10/17 10:31 PM f=1.01 /home/phillip/eagle/YAZ180_V2.1/YAZ180_V21.sch (Sheet: 3/7)

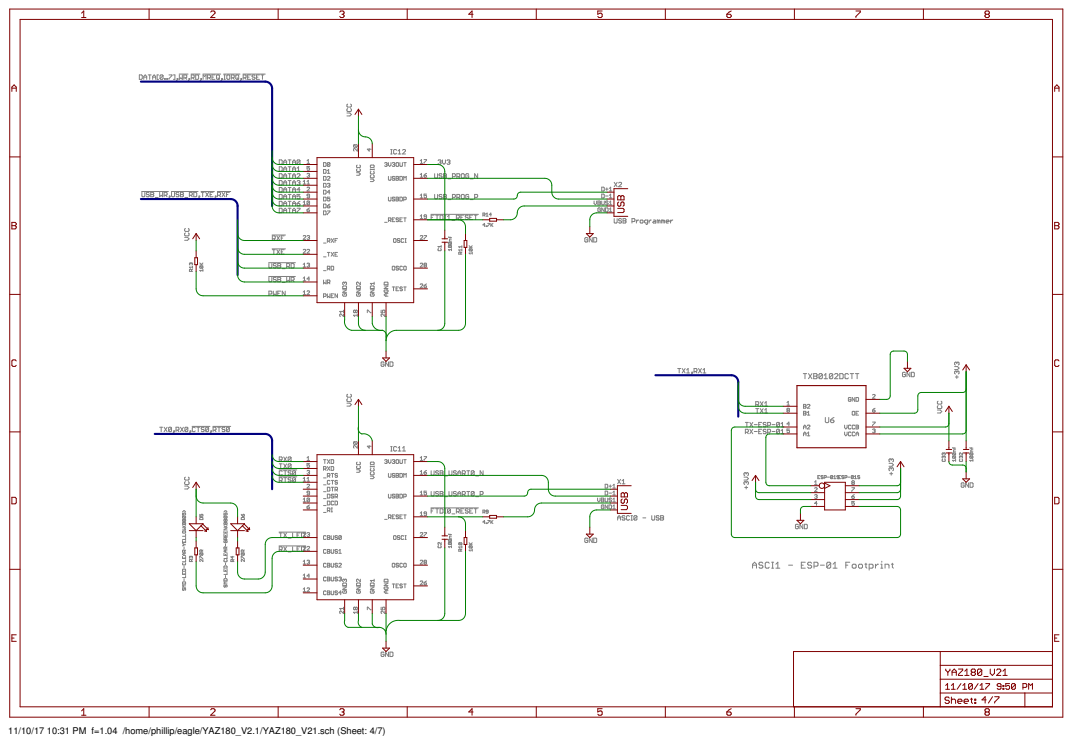
[picture p77: page 4]

11/10/17 10:31 PM f=1.04 /home/phillip/eagle/YAZ180_V2.1/YAZ180_V21.sch (Sheet: 4/7)

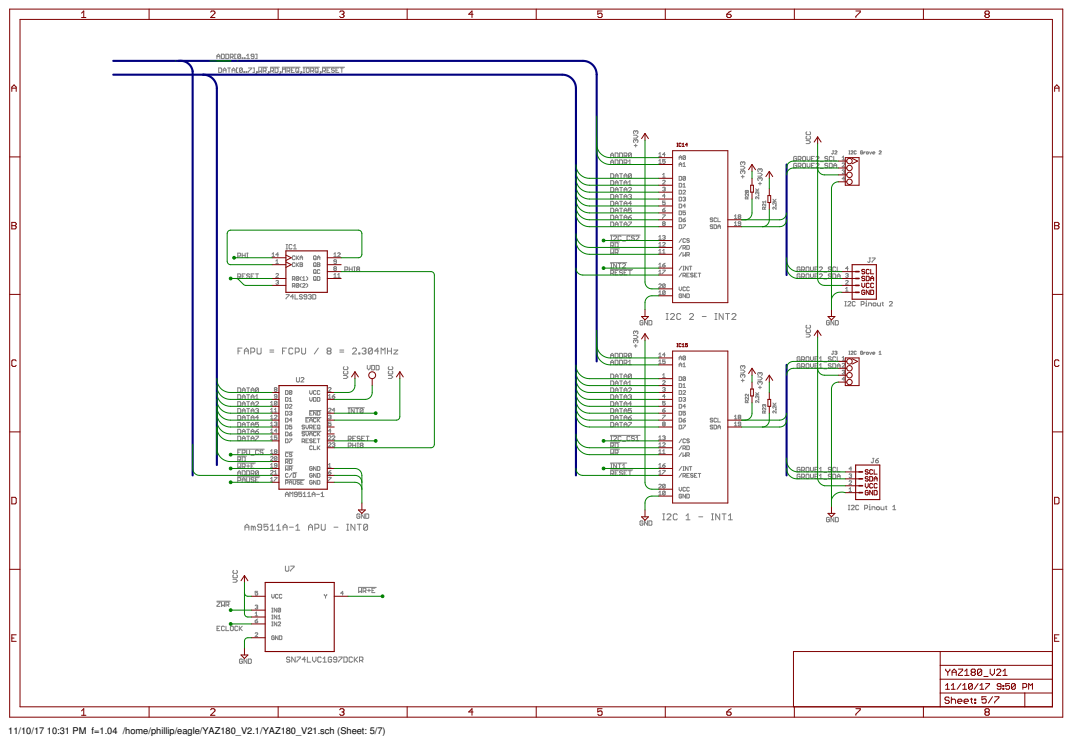
[picture p78: page 5]

11/10/17 10:31 PM f=1.04 /home/phillip/eagle/YAZ180_V2.1/YAZ180_V21.sch (Sheet: 5/7)

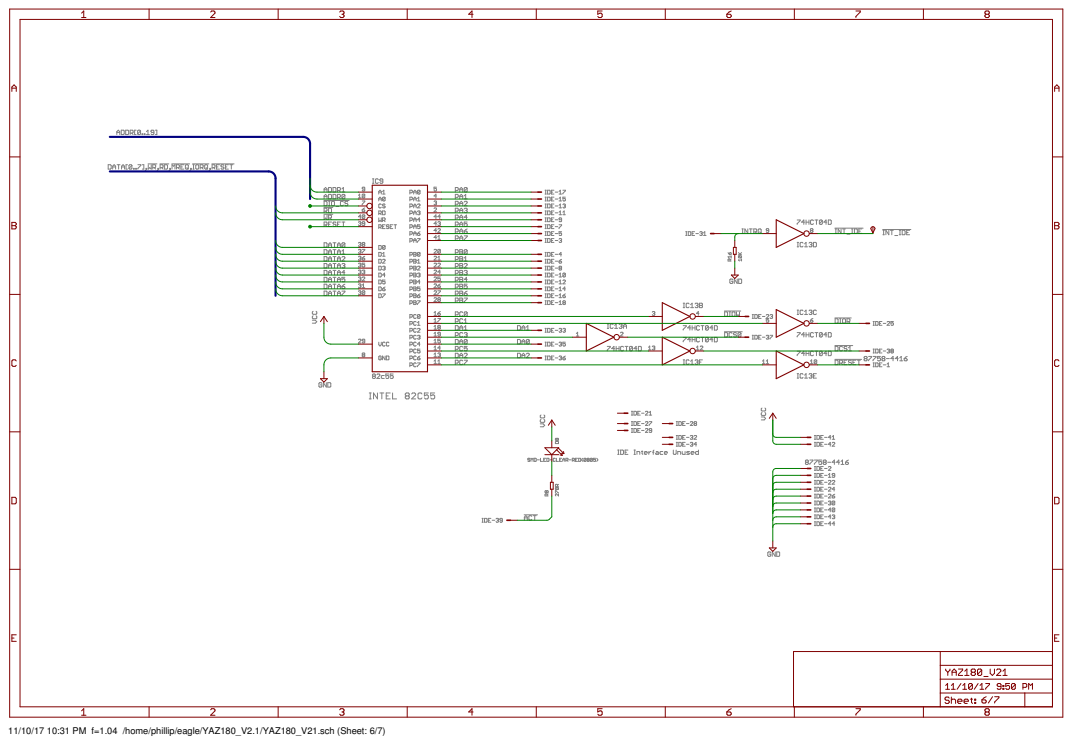
[picture p79: page 6]

11/10/17 10:31 PM f=1.04 /home/phillip/eagle/YAZ180_V2.1/YAZ180_V21.sch (Sheet: 6/7)

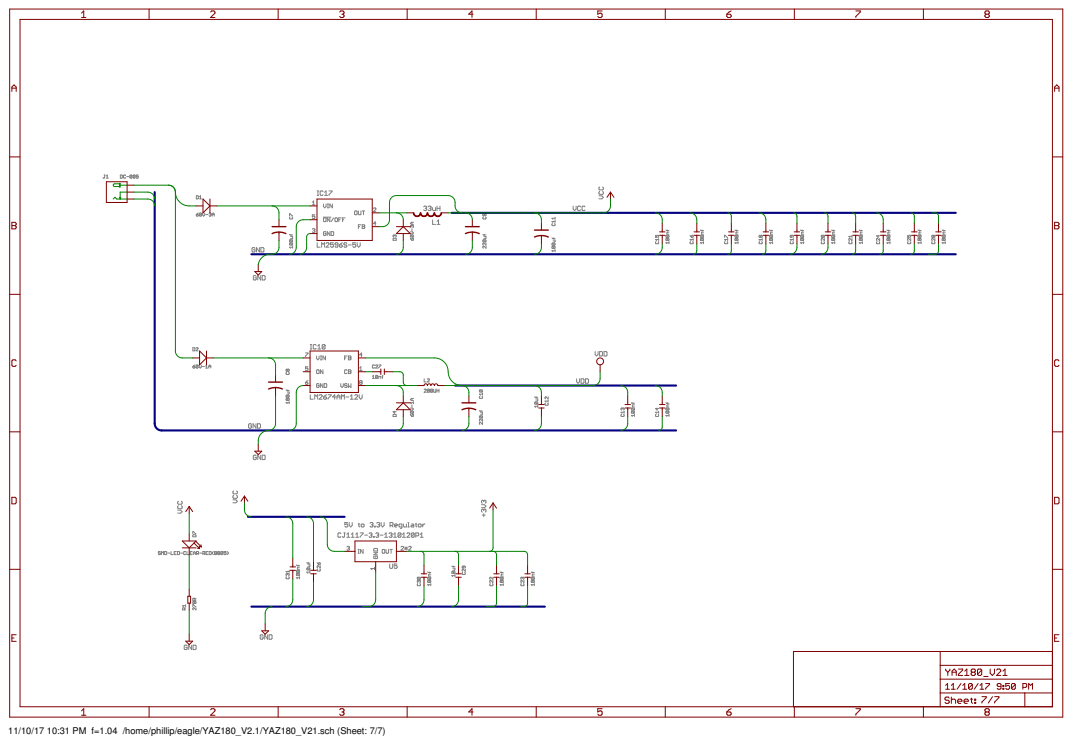
[picture p80: page 7]

11/10/17 10:31 PM f=1.04 /home/phillip/eagle/YAZ180_V2.1/YAZ180_V21.sch (Sheet: 7/7)
