feilipu/yaz180/docs/YAZ180_V22_Values.pdf

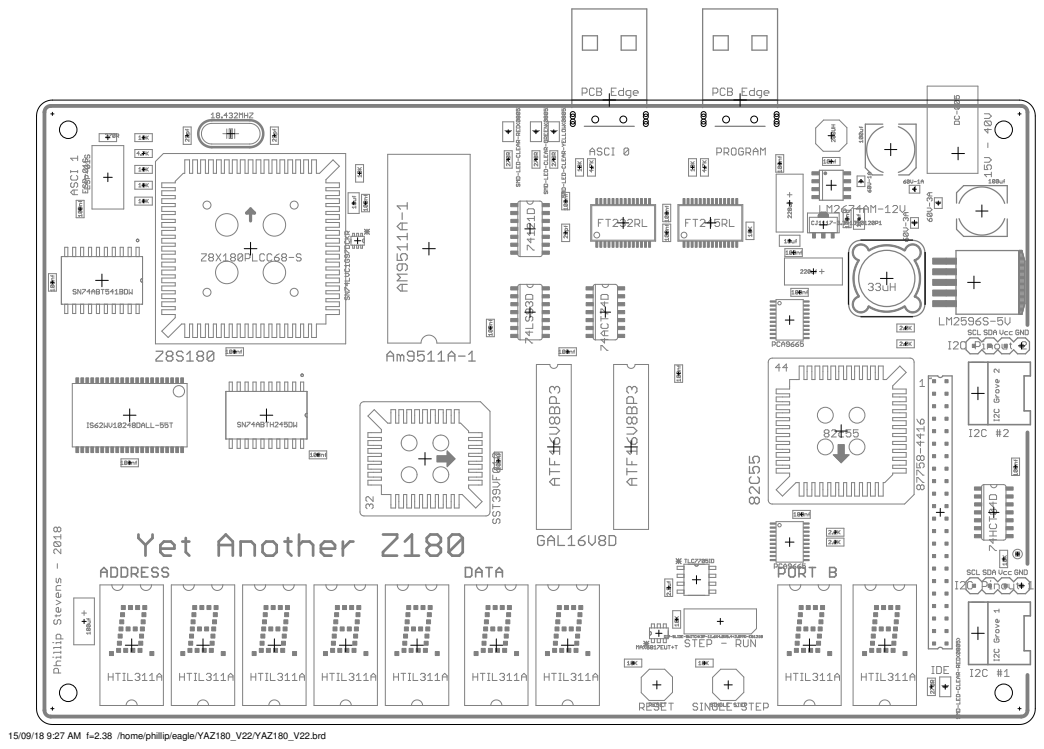
[picture p82: page 1]

15/09/18 9:27 AM f=2.38 /home/phillip/eagle/YAZ180_V22/YAZ180_V22.brd
