feilipu/yaz180/docs/YAZ180_V21_Names.pdf

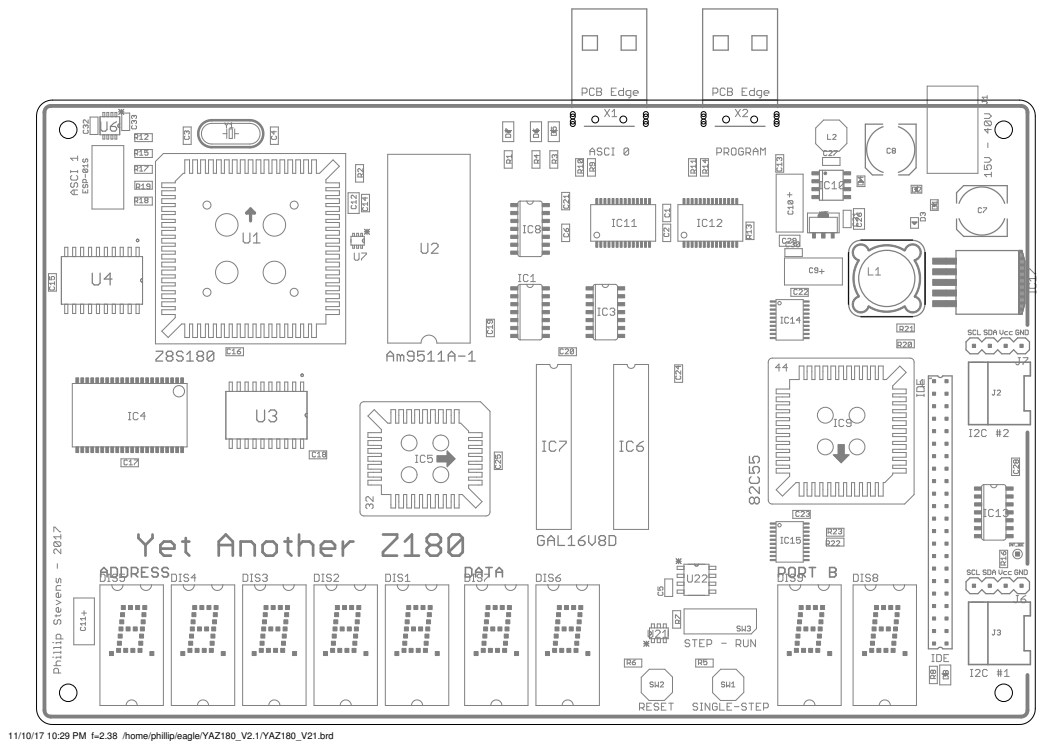
[picture p83: page 1]

11/10/17 10:29 PM f=2.38 /home/phillip/eagle/YAZ180_V2.1/YAZ180_V21.brd
