feilipu/yaz180/docs/Hi-Tech_C_Libraries/FLOAT/finc.asm

;	lfinc - floating increment
;	lfdec - floating decrement

	psect	text
	global	lfinc, lfdec, asfladd

lfinc:
	exx
	ld	hl,one
incdec:
	exx			;restore original hl
	ld	e,(hl)		;get left operand original value
	inc	hl
	ld	d,(hl)
	inc	hl
	ld	c,(hl)
	inc	hl
	ld	b,(hl)
	push	bc
	push	de		;save on the stack for 'ron
	dec	hl		;restore pointer value
	dec	hl
	dec	hl
	exx			;now pointer to right op
	ld	e,(hl)
	inc	hl
	ld	d,(hl)
	inc	hl
	ld	c,(hl)
	inc	hl
	ld	b,(hl)
	push	bc		;hi order word first
	push	de		;low order word second
	exx			;restore pointer to left op
	call	asfladd		;perform the addition
	pop	de		;pop original lo word
	pop	hl		;and high word
	ret			;and return with it in the right place

lfdec:
	exx
	ld	hl,mone		;get a minus one
	jp	incdec

	psect	data
one:
	deff	1.0
mone:
	deff	-1.0
